FibonacciSpiral/SAM/Documentation/MarketingRequirementsDesignSpecification.xlsx

Market Req and Design Spec
 | Document Number: |  | Revision: 1
 | Division: | STMS Team | Document Date: 02 September 2022
 | Project: | Single Channel Monitor | Project Start Date:
 | Originator: | Div Tummala
 | Circulation: | STMS Team
1 | Approvals
 | Title | Print Name | Signature | Date
2 | Related Documents
 | Document Number | Description
3 | Problem Statement
 | The Single Channel Monitor Box is intended to be used with Type K thermocouples allowing for digital read out with alarm functions to be utilized where-ever needed in system installs. Foremost intent is immediate use with FLEX series heaters where location and powering of the unit is intended to be in-line with the gas heater power. Where power to the heater can first go through the monitoring box and then to the heater to make powering nad connection easier. Ability to easily set the "set point" for alerting when falls below desired maintenance temperatures on site and by any user is intended. Small box shape with Neutrik leads in-out with power "passthrough" to enable easy use and installation. TC connection (type K) should also be so that the heater can easily be connected (in other words likely as a "lead" vs a panel mount).
4 | Function, Theory of Operation
 | The single channel monitor is intended to be directly connect to a FLEX heater solution. Ideally be small and light enough not to require mounting. If that is not feasible then mounting to pipework is next best option. If mounting to pipework is necessary then accommodation for airgap is needed and method to attach to pipework (straps or other such accessory add-on). Airgap is required as direct connection will result in high temperatures as there will be TMS on the line in majority if not all the installations and without an airgap the temperatures could get quite warm. The single channel monitor should have a display that shows temperature of the FLEX and a way to set the alert temperature without needing other devices if possible. If using another device is necessary to keep cost down (via a comm port or similar), then that capability needs to be included as a project deliverable and possibly be done via the TMS APP or some other readily available application using common connector cables readily available (non-custom connectors/cable assemblies requiring Edwards supply). There should be a modbus communication port to enable connection into another controller or monitoring system as needed by the customer (a way to allow multiple units connected into a single device may be needed as consideration - i.e. several units connected into an integrated system, STMS system, customer control system, etc) There also is needed a "dry contact" (relay open/closed circuit connection).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
5 | Cost Target(s), Expected Volumes
 | Description | Marketing Required | Marketing Desired | Design Specification | Design Review | Design Validation/Verification | Comments
5.1 | Production assembly cost | Less than $200 USD | Less than $150
5.2 | Expected volumes | 1st year: 100 to 1000
5.3
5.4
6 | Common Requirements
 | Description | Marketing Required | Marketing Desired | Design Specification | Design Review | Design Validation/Verification | Comments
6.1 | Device mounting | Device is light enough so no mounting is required. Add support brackets if deemed necessary but intended to be supported by the pipework with "warm/hot" pipes that could have external surface temperature as high as 70C in free air. Assume unistrut style mounting options for anything that is external to the pipe system - this option is not preferred Assume range of pipework if using the pipe as support mechanism Note: Insulation can be up to 25mm thick NW32-NW50 sizes being most common but can be bigger (ISO100mm in DSL sites) Several "strap" or mounting options may be required if mounting is needed and attached to pipe as preferred. | Attachement Mechanism that allows for air gap if needed and secures to pipework | 1.) Enclosure should include mounting slots or a mechanism that accomadates metal, cloth and velcro straps. 2.) Device with mounting accessories shall accomadate being secured to cylinderical surface diameters between 30mm and 250mm.
6.2 | Air gap | Air gap is required between Device and pipework to prevent conductive heat transfer to Device |  | 1.) Device when secured to a 85oC surface, no locations outside of the contact points shall be at > 35oC with an ambient temperature of 25oC
6.3 | Fans |  | Avoid using fans | 1.) Passive cooling of electronics. No fans.
6.4 | Display | Display temperature of attached Flex heater |  | 1.) 4 character alphanumeric LED display. 2.) Design a navigation menu that utilizes 4 characters. 3.) During normal operation 3 characters display numbers and the 4th character displays C (Centigrade) or F (Farenheit). 4.) Display should show an Alert when temperature below setpoint
 |  |  |  | "Menu" - menu "Set" - set / enter "setP" - setpoint "degU" - degrees units, C or F "ERR" - error "LowT" - temperature below setpoint "Ver" - firmware version "EXTR" - Device in external setup mode. For example when the device IP address needs to be configured.
6.5 | Communication 1 | Modus over TCP/IP |  | 1.) Send temperature data via TCP/IP. 2.) Physical connection via RJ45 port / ethernet cable. 3.) Accomadate multiple Devices connected via a commercial ethenet hub. 4.) Device IP address configurable via User laptop Cat5e ethernet cable.
6.6 | Communication 2 | Dry contacts |  | 1.) 2 position dry contact interface. i.e. No voltage or current allowed on these contacts. 2.) MCU controls a Normally Open relay that closes the 2 position (a short) when Device Temperature setpoint has reached. Open when Device loose power or Temperature setpoint has not reached.
6.7 | Poke Yoke | None required for this product design other than can readily be used with existing cable extension options for FLEX/SPOT products |  | 1.) ***See "Electrical Connectors" section below.
6.8 | Life cycle | Expectation is unit will have expected working life of 10yrs. Ability to warranty of up to 5yrs is preferred - standard Edwards warranty is 1yr but 5yrs is industry expectation. Dry contact cycle count estimated to be less than 200 cycles. Should only be activated on power up/power down during maintenance and rare alert incidents. |  | 1.) Dry contact relay MTBF > 1000 cycles. 2.) Device MTBF > 1 year
7 | Power Requirements
 | Description |  | Marketing Desired | Design Specification | Design Review | Design Validation/Verification | Comments
7.1 | FLEX heaters are designed to operate on 10A circuits so proper protection is required as needed depending on design against any faults that could occur with the monitor box internal circuits/assembly.
7.2 | Power should pass through the box unhindered to the heater even if the monitor box has a fault and self protects.
7.3 | Electrical connectors | Power interface: Neutrik CBC connectors Connectors shall not require special crimps/pin or specific tools for normal operation. TC: Type K mini-connector (same used on FLEX series) may be a "flying lead to enable easy connection to FLEX family of heaters and long enough to ensure power lead take the strain if something is snagged or pulled on | Dry Contact: any connector deemed suitable is fine as long as can have wires connected with readily available tools such as a screwdriver. No special crimps/pins requiring specific tools. TC: flying lead to enable easy connection to flex family of heaters and long enough to ensure power lead can take the strain if snagged or pulled on. Modbus port: any common connector or screw terminal connector can be used e.g., screw terminal connector or RJ45 as examples. Consider ease of cable procurement by customers | 1.) Power interface: Neutrik CBC NAC3MX-W for AC power into Device. Terminate inside the Device via ring terminal secured to a PCB mounted power tap. 2.) TC: Omega SMP-C-F (or similar) for leaded connector or PCB mounted Omega PCC-SMP-K (or similar). Overall BOM cost decides selection criteria. 3.) Modbus port: Board mounted RJ45 Shielded.
8 | Mechanical & Electrical Safety
 | Description | Marketing Required | Marketing Desired | Design Specification | Design Review | Design Validation/Verification | Comments
9 | Customer Interface(s)
 | Description | Marketing Required | Marketing Desired | Design Specification | Design Review | Design Validation/Verification | Comments
10 | Physical Appearance / Size
 | Description | Marketing Required | Marketing Desired | Design Specification | Design Review | Design Validation/Verification | Comments
 | Dimensions | 140mm long x 70mm wide x 70mm tall | (120mm long x 50mm wide x 50mm wide) or smaller | Less than (140mm long x 70mm wide x 70mm tall )
11 | Environment
 | Description | Marketing Required | Marketing Desired | Design Specification | Design Review | Design Validation/Verification | Comments
11.1 | Heater(s) | • Indoor use. • Altitude up to 2000m. • Temp range 5-40°C. • Max relative humidity 80% for temps up to 31°C decreasing linearly to 50% relative humidity at 40°C. • Mains supply fluctuations up to +/-10% of nominal. • Transient over voltages up to the levels of overvoltage cat II (these levels are typical for equipment supplied from the building wiring). • Applicable pollution degree of the intended environment (degree 2 in most cases). |  | • Indoor use. • Altitude up to 2000m. • Temp range 5-40°C. • Max relative humidity 80% for temps up to 31°C decreasing linearly to 50% relative humidity at 40°C. • Mains supply fluctuations up to +/-10% of nominal. • Transient over voltages up to the levels of overvoltage cat II (these levels are typical for equipment supplied from the building wiring). • Applicable pollution degree of the intended environment (degree 2 in most cases).
11.2 | Ingress Protection | IP44 | IP42 | 1.) Design and verify to meet IP44
12 | Certifications & Compliance
 | Description | Marketing Required | Marketing Desired | Design Specification | Design Review | Design Validation/Verification | Comments
12.1 | CE | Yes - Mandatory |  | LVD to EN60204
12.2 | RoHS | Yes - Mandatory |  | with exceptions
12.3 | China RoHS | Yes - Mandatory |  | with exceptions
12.4 | WEEE | Yes - Mandatory |  | No, not required
12.5 | UKCA |  |  | LVD to EN60204
12.6 | REACH |  |  | No listed hazardous materials
12.7 | UL Recognized | No
12.8 | SEMI S2-0712d | Yes
12.9 | SEMI S22 | Yes - But do not certify
13 | Equipment Compatibility
 | Description | Marketing Required | Marketing Desired | Design Specification | Design Review | Design Validation/Verification | Comments
 | Flex 50 gas heaters | yes
14 | Backward Compatibility
 | Description | Marketing Required | Marketing Desired | Design Specification | Design Review | Design Validation/Verification | Comments
14.1 | N/A | N/A | N/A
15 | Spares Requirements
 | Description | Marketing Required | Marketing Desired | Design Specification | Design Review | Design Validation/Verification | Comments
 | Spares | No maintenance is expected. If there are any "consumable parts" for overcurrent protection needed - plan for spares and documentation/method to replace needs to be planned in.
16 | Labeling and Marking
 | Description | Marketing Required | Marketing Desired | Design Specification | Design Review | Design Validation/Verification | Comments
 | Device label | Serialization: Does not have to be serialized in Edwards systems, but if possible would be nice for product quality investigations. Must be at least serialized at manufacturing site tied to its test results for traceability when needed. Part Number: Yes Certifications: Yes (CE) Country of Origin: Yes Color Identification: N/A |  | 1.) Devices are to be serialized at manufacturing site. 2.) Device label design should include: - Model Number - Serial Number - Country of Origin - CE marking
17 | Software and APPs Req.
 | Description |  | Marketing Desired | Design Specification | Design Review | Design Validation/Verification | Comments
17.1 | STMS controllers |  | May be desired to "see" the monitor on HMI and or EdCentra in future Not required to be delivered at project end but plan on how it could be seen/read by main controller os something to consider alternate is ability to see on HMI Provision to see multiple monitors on single controller or HMI needs consideration
17.2 | HMI |  | See controller description for potential need to "see/monitor" multiple monitor boxes by our HMI Consideration how to do this is preferred Ultimate goal if for EdCentra visibility and display remotely if feasible and a plan to get us there considered in design in some way.
17.3 | Support applications | Added to STMS APP once FLEX heater accessories are added as another option to build into BOM generation
18 | Functional Test
 | Description | Marketing Required | Marketing Desired | Design Specification | Design Review | Design Validation/Verification | Comments
18.1 | Functional Test | 1.) Display correct temperature. 2.) Alert temperature setting. 3.) Alert dry contact. - open on lower temperature - closed at higher temperature - cycle capability back and forth 4.) Modbus communication. - temperature reading - alert state - alert set point - If allowed to "write" over Modbus -- set new alert temperature 5.) Temperature during operation. - inside unit for critical component -- while mounted if planned to be attached to pipework - outside unit (if mounted on pipework) -- at various interface points to ensure within rating of enclosure 6.) Time to set and reset alerts. 7.) Power consumption during use
18.2
19 | Factory Acceptance Testing
 | Description | Marketing Required | Marketing Desired | Design Specification | Design Review | Design Validation/Verification | Comments
20 | Reliability
 | Description | Marketing Required | Marketing Desired | Design Specification | Design Review | Design Validation/Verification | Comments
21 | Packaging Specification
 | Description | Marketing Required | Marketing Desired | Design Specification | Design Review | Design Validation/Verification | Comments
22 | Accessories
 | Description | Part Number (if available) | Edwards Description | Design Specification | Design Review | Design Validation/Verification | Comments
23 | Documentation
 | Description | Marketing Required | Marketing Desired | Design Specification | Design Review | Design Validation/Verification | Comments
 |  | 1.)Technical drawings and 3D models of components and subassembly 2.) Maintenance/Service documentation 3.) Test schedule(s) 4.) Wiring schematics 5.) Compliance 6.) Manual 7.) Manufacturing assembly or final test as required
 | Revision History
Rev | Date | Description of Changes | Originator | Approver
