FibonacciSpiral/SAM/SingleChannelMonitorBox/src/ModbusServerTCP/Include/mbport.h

/* 
 * FreeModbus Libary: A portable Modbus implementation for Modbus ASCII/RTU.
 * Copyright (c) 2006-2018 Christian Walter <cwalter@embedded-solutions.at>
 * All rights reserved.
 *
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
 */

#ifndef _MB_PORT_H
#define _MB_PORT_H

#ifdef __cplusplus
PR_BEGIN_EXTERN_C
#endif

#include "port.h"

/* FreeRTOS includes. */
#include <FreeRTOS.h>
#include "task.h"
#include "timers.h"
#include "queue.h"
#include "semphr.h"

/* FreeRTOS+TCP includes. */
#include "FreeRTOS_IP.h"
#include "FreeRTOS_Sockets.h"


/* ----------------------- Type definitions ---------------------------------*/

typedef enum
{
    EV_READY,                   /*!< Startup finished. */
    EV_FRAME_RECEIVED,          /*!< Frame received. */
    EV_EXECUTE,                 /*!< Execute function. */
    EV_FRAME_SENT               /*!< Frame sent. */
} eMBEventType;

/*! \ingroup modbus
 * \brief Parity used for characters in serial mode.
 *
 * The parity which should be applied to the characters sent over the serial
 * link. Please note that this values are actually passed to the porting
 * layer and therefore not all parity modes might be available.
 */
typedef enum
{
    MB_PAR_NONE,                /*!< No parity. */
    MB_PAR_ODD,                 /*!< Odd parity. */
    MB_PAR_EVEN                 /*!< Even parity. */
} eMBParity;

/* Defines */

#define mainMB_TASK_PRIORITY    ( tskIDLE_PRIORITY + 3 )
#define mainMB_SERVER_STACK_SIZE configMINIMAL_STACK_SIZE * 6
#define PROG                    "FreeModbus"
#define REG_INPUT_START         1000
#define REG_INPUT_NREGS         4
#define REG_HOLDING_START       2000
#define TEMP_HOLDING_REG		REG_HOLDING_START
#define SETPOINT_HOLDING_REG	(REG_HOLDING_START + 1)
#define TEMP_SYSTEM_HOLDING_REG (REG_HOLDING_START + 2)
#define REG_HOLDING_NREGS       130
#define SYS_MBOX_SIZE           ( 16 )
/** Return code for timeouts from sys_arch_mbox_fetch and sys_arch_sem_wait */
#define SYS_ARCH_TIMEOUT 0xffffffff
#define MB_POLL_CYCLETIME       100     /* Poll cycle time is 100ms */

/* ----------------------- More Defines ------------------------------------------*/
#define MB_PDU_SIZE_MAX     253 /*!< Maximum size of a PDU. */
#define MB_PDU_SIZE_MIN     1   /*!< Function Code */
#define MB_PDU_FUNC_OFF     0   /*!< Offset of function code in PDU. */
#define MB_PDU_DATA_OFF     1   /*!< Offset for response data in PDU. */

/* ----------------------- Static variables ---------------------------------*/
extern USHORT   usRegInputStart;
extern USHORT   usRegInputBuf[REG_INPUT_NREGS];
extern USHORT   usRegHoldingStart;
extern USHORT   usRegHoldingBuf[REG_HOLDING_NREGS];
extern TaskHandle_t xMBTaskHandle;

/* ----------------------- Supporting functions -----------------------------*/
BOOL            xMBPortEventInit( void );

BOOL            xMBPortEventPost( eMBEventType eEvent );

BOOL            xMBPortEventGet(  /*@out@ */ eMBEventType * eEvent );

/* ----------------------- Serial port functions ----------------------------*/

BOOL            xMBPortSerialInit( UCHAR ucPort, ULONG ulBaudRate,
                                   UCHAR ucDataBits, eMBParity eParity );

void            vMBPortClose( void );

void            xMBPortSerialClose( void );

void            vMBPortSerialEnable( BOOL xRxEnable, BOOL xTxEnable );

BOOL            xMBPortSerialGetByte( CHAR * pucByte );

BOOL            xMBPortSerialPutByte( CHAR ucByte );

/* ----------------------- Timers functions ---------------------------------*/
BOOL            xMBPortTimersInit( USHORT usTimeOut50us );

void            xMBPortTimersClose( void );

void            vMBPortTimersEnable( void );

void            vMBPortTimersDisable( void );

void            vMBPortTimersDelay( USHORT usTimeOutMS );

/* ----------------------- Callback for the protocol stack ------------------*/

/*!
 * \brief Callback function for the porting layer when a new byte is
 *   available.
 *
 * Depending upon the mode this callback function is used by the RTU or
 * ASCII transmission layers. In any case a call to xMBPortSerialGetByte()
 * must immediately return a new character.
 *
 * \return <code>TRUE</code> if a event was posted to the queue because
 *   a new byte was received. The port implementation should wake up the
 *   tasks which are currently blocked on the eventqueue.
 */
extern          BOOL( *pxMBFrameCBByteReceived ) ( void ); //These are only needed if you are using modbus over serial

extern          BOOL( *pxMBFrameCBTransmitterEmpty ) ( void );

extern          BOOL( *pxMBPortCBTimerExpired ) ( void );

/* ----------------------- TCP port functions -------------------------------*/
BOOL            xMBTCPPortInit( USHORT usTCPPort );

void            vMBTCPPortClose( void );

void            vMBTCPPortDisable( void );

BOOL            xMBTCPPortGetRequest( UCHAR **ppucMBTCPFrame, USHORT * usTCPLength );

BOOL            xMBTCPPortSendResponse( const UCHAR *pucMBTCPFrame, USHORT usTCPLength );


/* ----------------------- prototypes -------------------------------*/
void vMBServerTask( void *arg );
static void mbServerConnectionInstance( void *pvParameters );
static void mbConnectionListeningTask( void *pvParameters );
void closeDownModbus(void);

//Queue RX buffer for traffic coming in
struct receiveStructure {
	uint8_t rxBuffer[MB_PDU_SIZE_MAX + 1];
	uint32_t size;
	};
	
//Queue TX buffer for traffic going out

struct transmitStructure {
	uint8_t * txBuffer;
	uint32_t size;
	};
	

#ifdef __cplusplus
PR_END_EXTERN_C
#endif
#endif
