FibonacciSpiral/SAM/SingleChannelMonitorBox/src/hr_gettime.c

/*
    FreeRTOS V9.0.0 - Copyright (C) 2016 Real Time Engineers Ltd.
    All rights reserved

    VISIT http://www.FreeRTOS.org TO ENSURE YOU ARE USING THE LATEST VERSION.

    This file is part of the FreeRTOS distribution.

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
    ***************************************************************************
    >>!   NOTE: The modification to the GPL is included to allow you to     !<<
    >>!   distribute a combined work that includes FreeRTOS without being   !<<
    >>!   obliged to provide the source code for proprietary components     !<<
    >>!   outside of the FreeRTOS kernel.                                   !<<
    ***************************************************************************

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
    ***************************************************************************
     *                                                                       *
     *    FreeRTOS provides completely free yet professionally developed,    *
     *    robust, strictly quality controlled, supported, and cross          *
     *    platform software that is more than just the market leader, it     *
     *    is the industry's de facto standard.                               *
     *                                                                       *
     *    Help yourself get started quickly while simultaneously helping     *
     *    to support the FreeRTOS project by purchasing a FreeRTOS           *
     *    tutorial book, reference manual, or both:                          *
     *    http://www.FreeRTOS.org/Documentation                              *
     *                                                                       *
    ***************************************************************************

    http://www.FreeRTOS.org/FAQHelp.html - Having a problem?  Start by reading
    the FAQ page "My application does not run, what could be wrong?".  Have you
    defined configASSERT()?

    http://www.FreeRTOS.org/support - In return for receiving this top quality
    embedded software for free we request you assist our global community by
    participating in the support forum.

    http://www.FreeRTOS.org/training - Investing in training allows your team to
    be as productive as possible as early as possible.  Now you can receive
    FreeRTOS training directly from Richard Barry, CEO of Real Time Engineers
    Ltd, and the world's leading authority on the world's leading RTOS.

    http://www.FreeRTOS.org/plus - A selection of FreeRTOS ecosystem products,
    including FreeRTOS+Trace - an indispensable productivity tool, a DOS
    compatible FAT file system, and our tiny thread aware UDP/IP stack.

    http://www.FreeRTOS.org/labs - Where new FreeRTOS products go to incubate.
    Come and try FreeRTOS+TCP, our new open source TCP/IP stack for FreeRTOS.

    http://www.OpenRTOS.com - Real Time Engineers ltd. license FreeRTOS to High
    Integrity Systems ltd. to sell under the OpenRTOS brand.  Low cost OpenRTOS
    licenses offer ticketed support, indemnification and commercial middleware.

    http://www.SafeRTOS.com - High Integrity Systems also provide a safety
    engineered and independently SIL3 certified version for use in safety and
    mission critical applications that require provable dependability.

    1 tab == 4 spaces!
*/

/* High resolution timer functions - used for logging only. */

/* Standard includes. */
#include <stdint.h>
#include <stdio.h>
#include <stdlib.h>

/* FreeRTOS includes. */
#include "FreeRTOS.h"
#include "task.h"
#include "queue.h"

/* Atmel includes. */
#include "board.h"
#include "tc.h"
#include "hr_gettime.h"
#include "sam4s/sysclk.h"

/* The TC interrupt will become active as little as possible: every half
minute. */
#define hrSECONDS_PER_INTERRUPT		30ul
#define hrMICROSECONDS_PER_SECOND	1000000ull

/*-----------------------------------------------------------*/

/* Timer interrupt handler. */
//void TC0_Handler ( void );

/*-----------------------------------------------------------*/

/* The timer channel to use. */
static const uint32_t ulTCChannel = 0;

/* Interrupt count. */
static uint32_t ulInterruptCount;

/*-----------------------------------------------------------*/

void vStartHighResolutionTimer( void )
{
	/* Timer initialisation. */
	tc_init( TC0, ulTCChannel, TC_CMR_TCCLKS_TIMER_CLOCK1 | TC_CMR_WAVSEL_UP_RC | TC_CMR_WAVE );
	tc_write_rc( TC0, ulTCChannel, ( hrSECONDS_PER_INTERRUPT * sysclk_get_cpu_hz() ) - 1ul );
	tc_start( TC0, ulTCChannel );

	NVIC_SetPriority( TC0_IRQn, configLIBRARY_MAX_SYSCALL_INTERRUPT_PRIORITY );
	NVIC_EnableIRQ( ( IRQn_Type ) TC0_IRQn );

	/* Enable this TC timer channel. */
	tc_enable_interrupt( TC0, ulTCChannel, TC_IER_CPCS );
}
/*-----------------------------------------------------------*/

void TC0_Handler( void )
{
	if( ( TC0->TC_CHANNEL[ ulTCChannel ].TC_SR & TC_SR_CPCS ) != 0 )
	{
		ulInterruptCount++;
	}
}
/*-----------------------------------------------------------*/

uint64_t ullGetHighResolutionTime( void )
{
static uint32_t ulCPUTicksPer_us = 0ul;
uint32_t ulCounts[2];
uint32_t ulSlowCount;
uint64_t ullReturn;


	if( ulCPUTicksPer_us == 0ul )
	{
		/* Calculate the number of CPU ticks per second. */
		ulCPUTicksPer_us = ( uint32_t ) ( ( sysclk_get_cpu_hz() + ( hrMICROSECONDS_PER_SECOND / 2 ) ) / hrMICROSECONDS_PER_SECOND );
	}

	for( ;; )
	{
		ulCounts[ 0 ] = tc_read_cv( TC0, ulTCChannel );
		ulSlowCount = ulInterruptCount;
		ulCounts[ 1 ] = tc_read_cv( TC0, ulTCChannel );

		if( ulCounts[ 1 ] >= ulCounts[ 0 ] )
		{
			/* TC0_Handler() has not occurred in between. */
			break;
		}
	}
	ullReturn = ( uint64_t )ulSlowCount * hrSECONDS_PER_INTERRUPT * hrMICROSECONDS_PER_SECOND + ( ulCounts[ 1 ] / ulCPUTicksPer_us );

	return ullReturn;
}
